wodowiesel/SW-Meter/docs/layers/swmeter-F_Cu.pdf

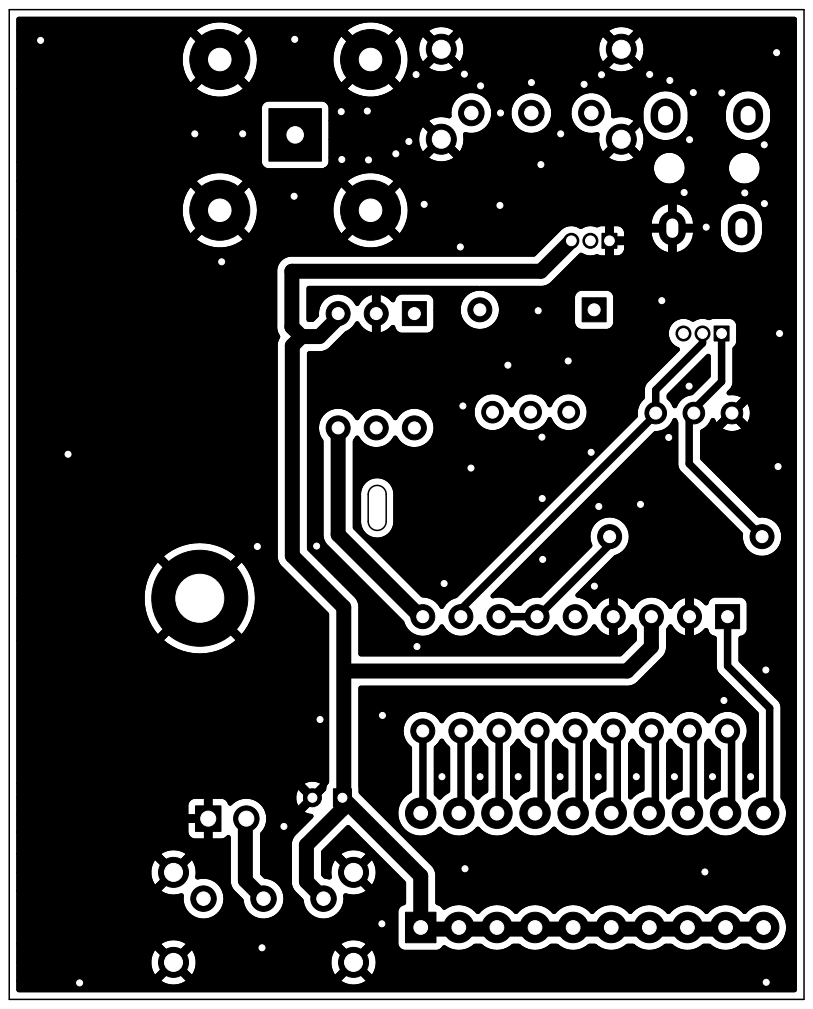
[picture p13: page 1]

File: swmeter.kicad_pcb Sheet: þÿ© WodoWiesel

Id: 1/1 Title: SW-Meter
