wodowiesel/SW-Meter/docs/layers/swmeter-F_Mask.pdf

File: swmeter.kicad_pcb Sheet: þÿ© WodoWiesel

Id: 1/1 Title: SW-Meter
