wodowiesel/SW-Meter/docs/layers/swmeter-Nutzer_4.pdf

File: swmeter.kicad_pcb Sheet: þÿ© WodoWiesel

Id: 1/1 Title: SW-Meter
