wodowiesel/SW-Meter/docs/layers/swmeter-User_Comments.pdf

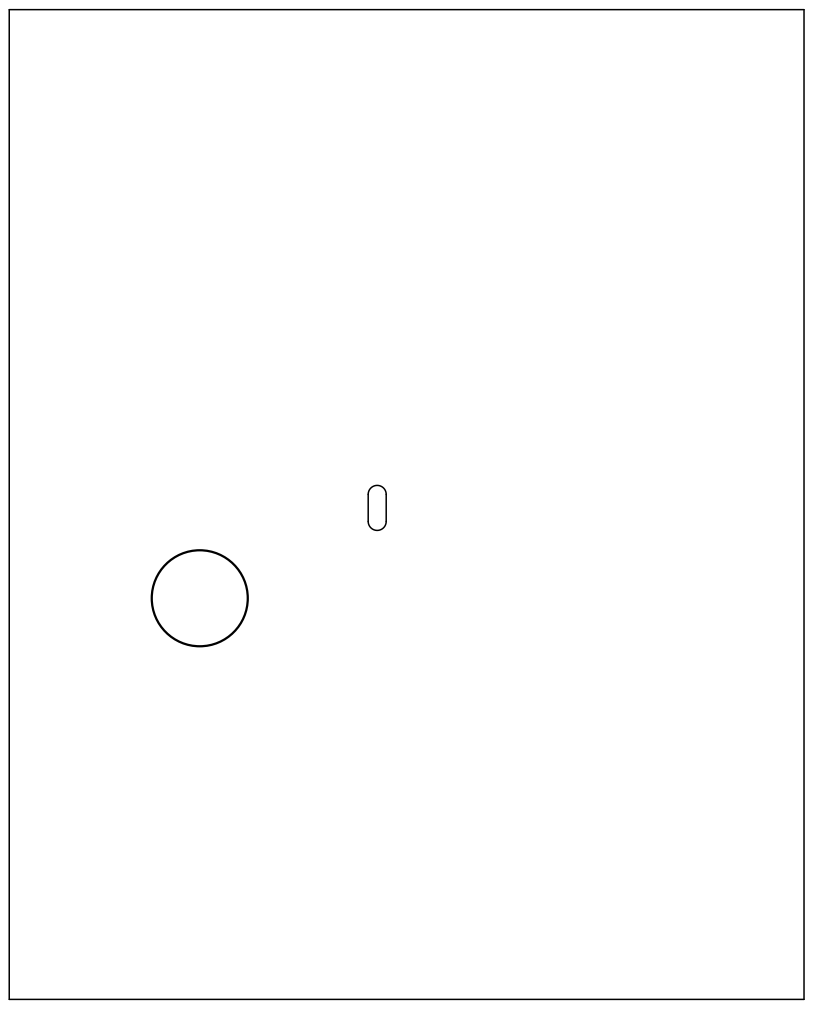
[picture p14: page 1]

File: swmeter.kicad_pcb Sheet: þÿ© WodoWiesel

Id: 1/1 Title: SW-Meter
