wodowiesel/SW-Meter/docs/layers/swmeter-User_Eco2.pdf

File: swmeter.kicad_pcb Sheet: þÿ© WodoWiesel

Id: 1/1 Title: SW-Meter
