wodowiesel/SW-Meter/docs/layers/swmeter-F_Fab.pdf

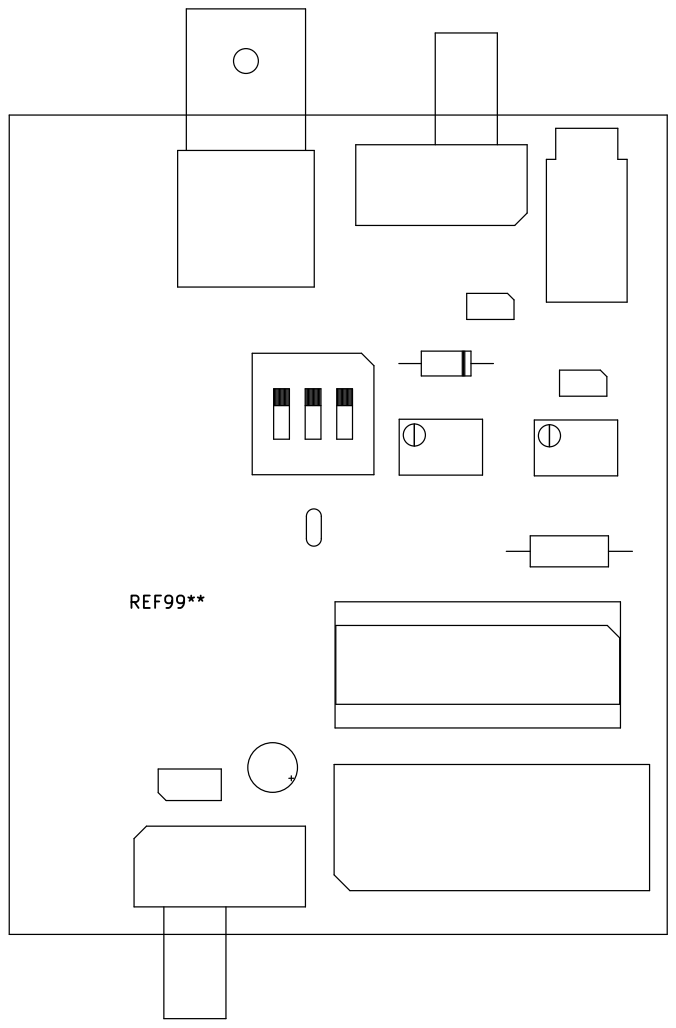
[picture p17: page 1]

Id: 1/1 Title: SW-Meter
