wodowiesel/SW-Meter/docs/layers/swmeter-F_Silkscreen.pdf

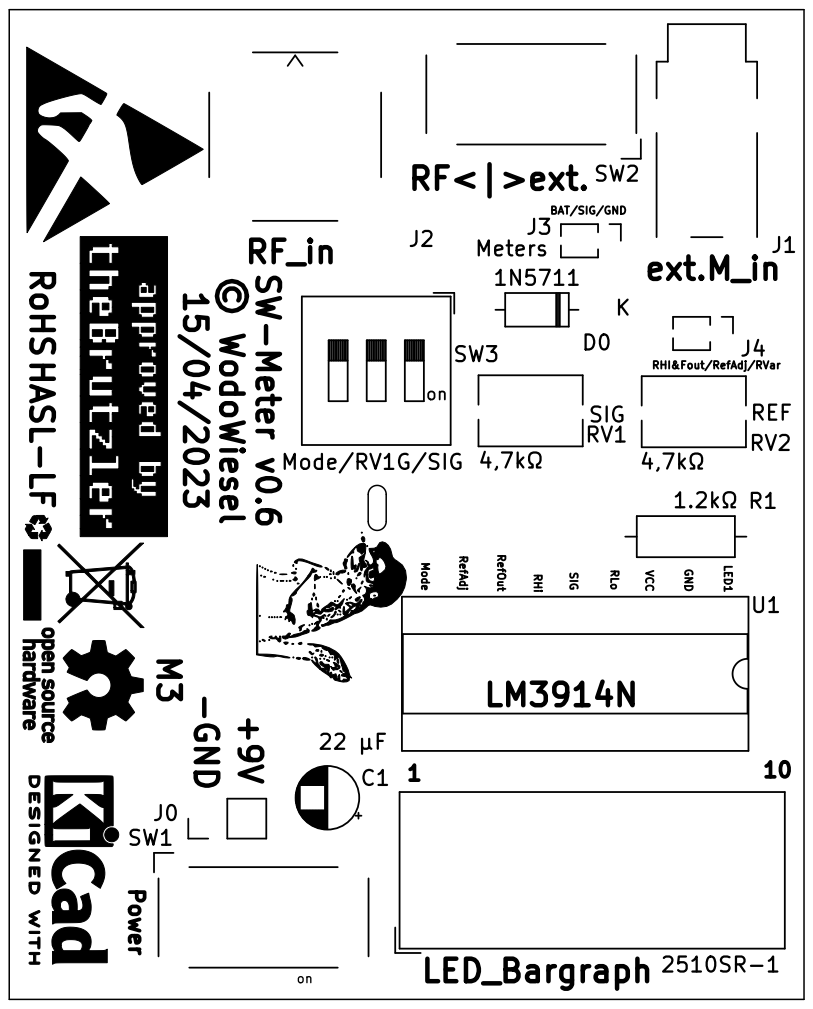
[picture p18: page 1]

Id: 1/1 Title: SW-Meter
