wodowiesel/SW-Meter/docs/layers/swmeter-User_Drawings.pdf

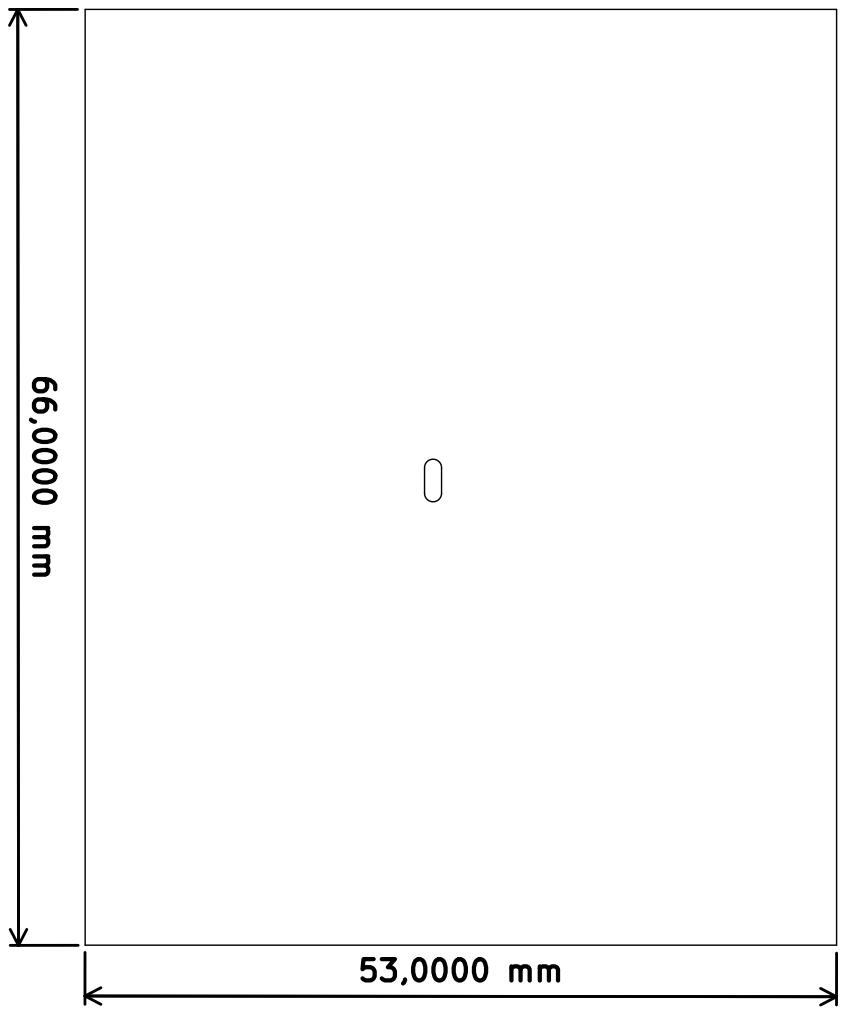
[picture p19: page 1]

Id: 1/1 Title: SW-Meter
